neyoyoyminoy/PalletPortal/3Dprinting/buttonHousingv2.stl

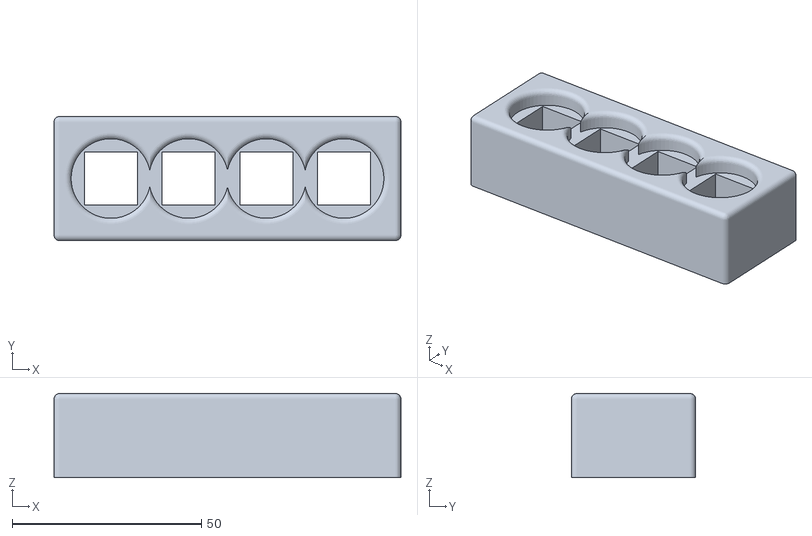
[picture p16: CAD file, 2025-10-09]
3Dprinting/buttonHousingv2.stl
91.6 x 32.8 x 22.2
