neyoyoyminoy/PalletPortal/3Dprinting/buttonCapv4.stl

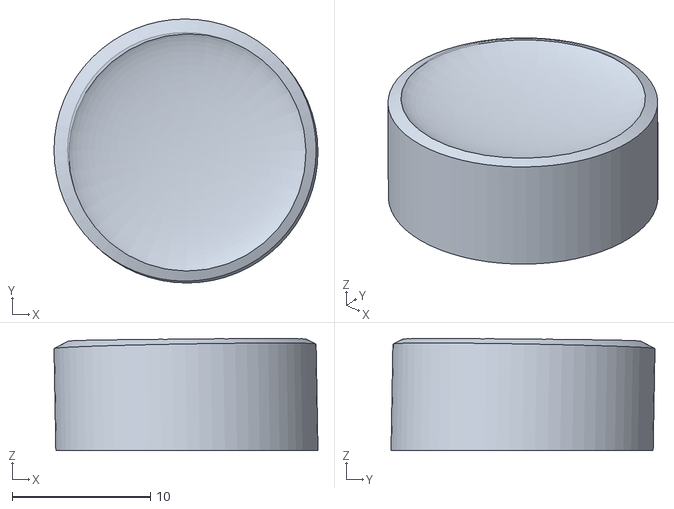
[picture p17: CAD file, 2025-10-09]
3Dprinting/buttonCapv4.stl
19.1 x 19.1 x 8.10
