neyoyoyminoy/PalletPortal/3Dprinting/buttonCapv2.stl

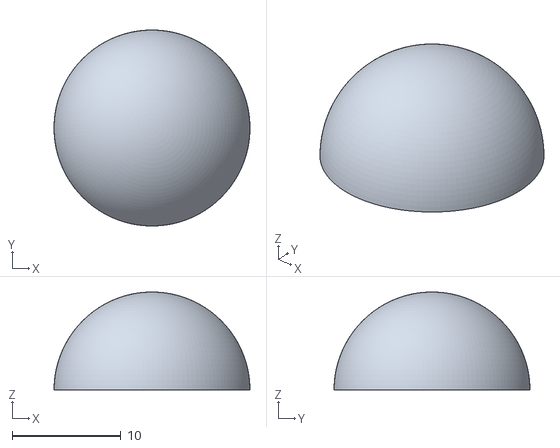
[picture p18: CAD file, 2025-10-09]
3Dprinting/buttonCapv2.stl
18.0 x 18.0 x 9.00
